zanedrys/IPAD/Polargraph/Polargraph 2017-11-01/processing-source/Processing libraries/diewald_CV_kit/examples/colorize_pattern/data/diewald_CV_kit_pattern4colorizer_v6.jpg

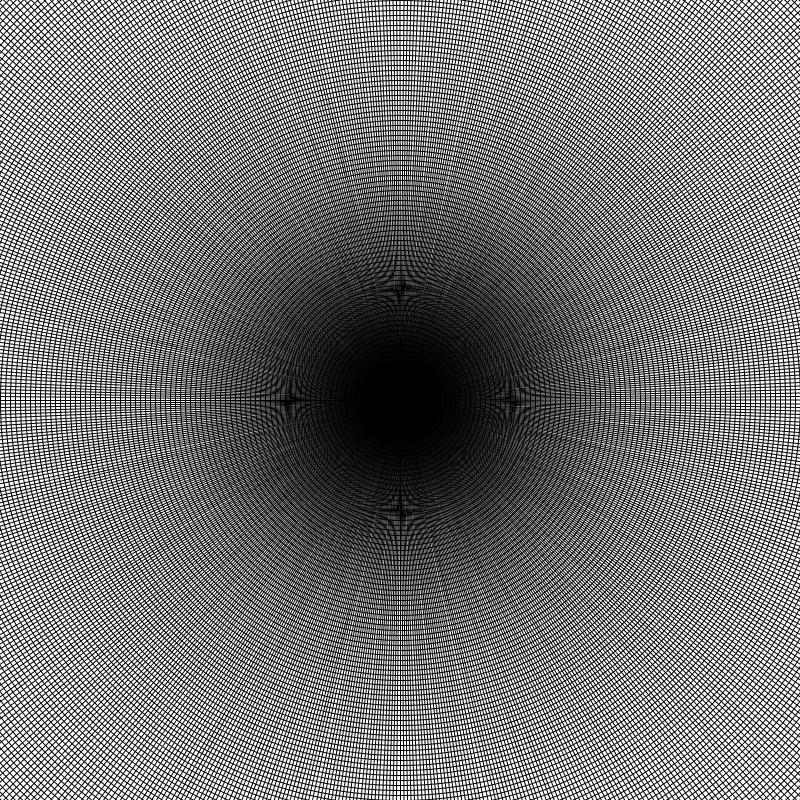
Polargraph/Polargraph 2017-11-01/processing-source/Processing libraries/diewald_CV_kit/examples/colorize_pattern/data/diewald_CV_kit_pattern4colorizer_v6.jpg
