zanedrys/IPAD/Polargraph/Polargraph 2017-11-01/processing-source/Processing libraries/diewald_CV_kit/examples/extract_hands/data/diewald_CV_kit_two_hands_640x480.jpg

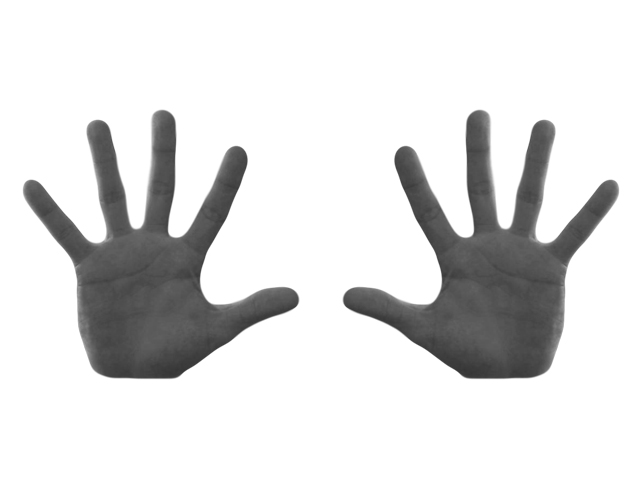
Polargraph/Polargraph 2017-11-01/processing-source/Processing libraries/diewald_CV_kit/examples/extract_hands/data/diewald_CV_kit_two_hands_640x480.jpg
