zanedrys/IPAD/Polargraph/Polargraph 2017-11-01/processing-source/Processing libraries/diewald_CV_kit/examples/kinect_3D/SCREENSHOT/diewald_CV_kit_kinect_3D_hand.jpg

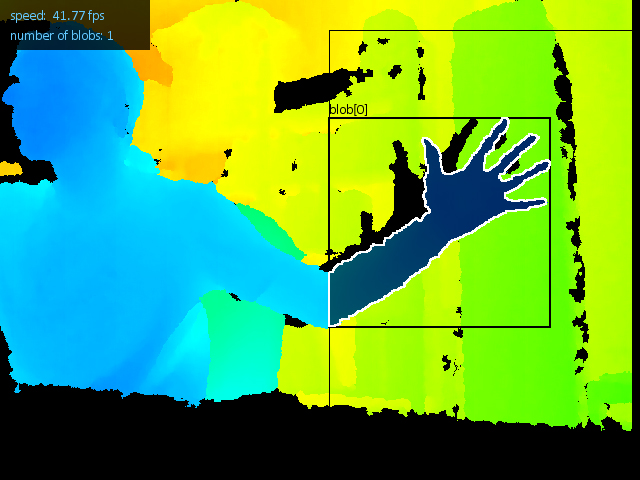
Polargraph/Polargraph 2017-11-01/processing-source/Processing libraries/diewald_CV_kit/examples/kinect_3D/SCREENSHOT/diewald_CV_kit_kinect_3D_hand.jpg
