zanedrys/IPAD/Polargraph/Polargraph 2017-11-01/processing-source/Processing libraries/diewald_CV_kit/examples/kinect_3D_pointcloud/data/diewald_CV_kit_marker_domino_4.jpg

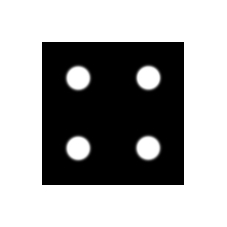
Polargraph/Polargraph 2017-11-01/processing-source/Processing libraries/diewald_CV_kit/examples/kinect_3D_pointcloud/data/diewald_CV_kit_marker_domino_4.jpg
