zanedrys/IPAD/Polargraph/Polargraph 2017-11-01/processing-source/Processing libraries/diewald_CV_kit/examples/simple_blobs/SCREENSHOT/diewald_CV_kit_simple_blobs.jpg

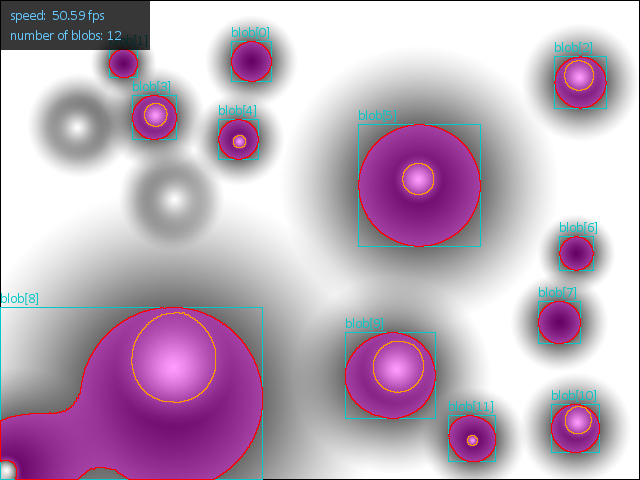
Polargraph/Polargraph 2017-11-01/processing-source/Processing libraries/diewald_CV_kit/examples/simple_blobs/SCREENSHOT/diewald_CV_kit_simple_blobs.jpg
