zanedrys/IPAD/Polargraph/Polargraph 2017-11-01/processing-source/Processing libraries/diewald_CV_kit/examples/webcam_marker_domino/data/diewald_CV_kit_marker_domino_1.jpg

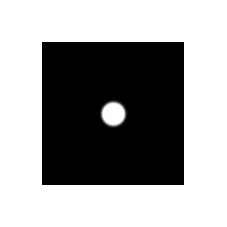
Polargraph/Polargraph 2017-11-01/processing-source/Processing libraries/diewald_CV_kit/examples/webcam_marker_domino/data/diewald_CV_kit_marker_domino_1.jpg
