zanedrys/IPAD/Processing 2.2.1/processing-2.2.1/modes/java/examples/Basics/Image/Alphamask/data/mask.jpg

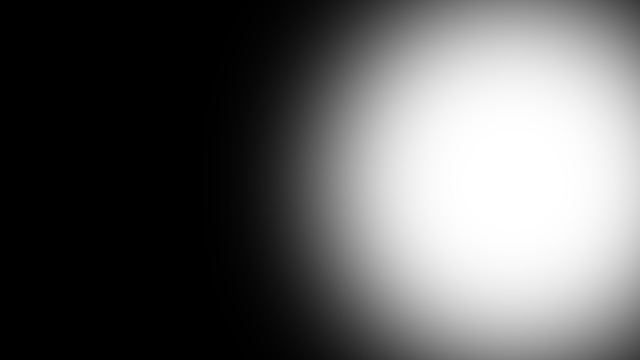
Processing 2.2.1/processing-2.2.1/modes/java/examples/Basics/Image/Alphamask/data/mask.jpg
