zanedrys/IPAD/Processing 2.2.1/processing-2.2.1/modes/java/examples/Basics/Image/Alphamask/data/moonwalk.jpg

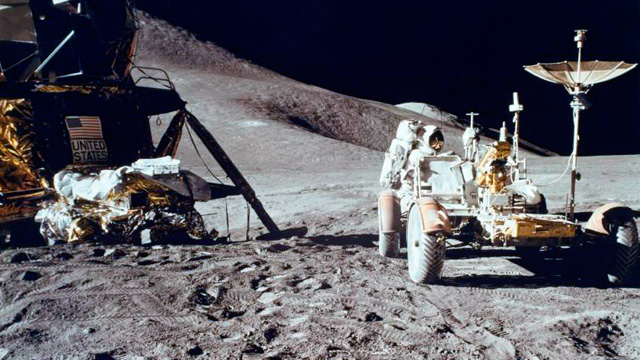
Processing 2.2.1/processing-2.2.1/modes/java/examples/Basics/Image/Alphamask/data/moonwalk.jpg
