zanedrys/IPAD/Processing 2.2.1/processing-2.2.1/modes/java/examples/Basics/Image/RequestImage/data/PT_anim0004.gif

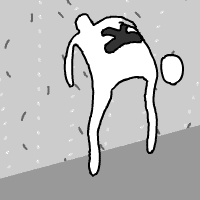
Processing 2.2.1/processing-2.2.1/modes/java/examples/Basics/Image/RequestImage/data/PT_anim0004.gif
