zanedrys/IPAD/Processing 2.2.1/processing-2.2.1/modes/java/examples/Basics/Shape/LoadDisplayOBJ/data/rocket.png

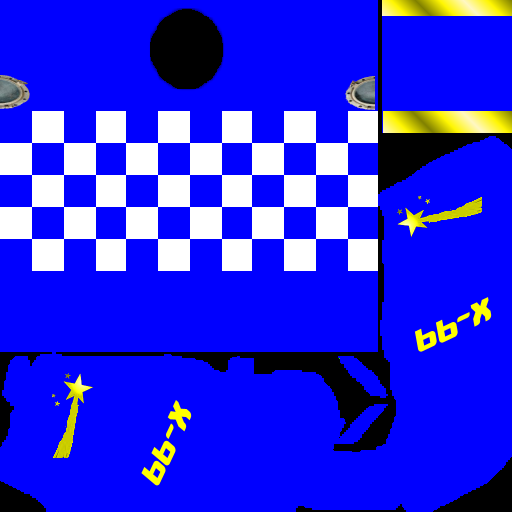
Processing 2.2.1/processing-2.2.1/modes/java/examples/Basics/Shape/LoadDisplayOBJ/data/rocket.png
