zanedrys/IPAD/Processing 2.2.1/processing-2.2.1/modes/java/examples/Books/Nature of Code/chp4_systems/Exercise_4_12_ArrayofImages/data/reflection.png

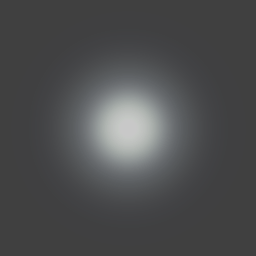
Processing 2.2.1/processing-2.2.1/modes/java/examples/Books/Nature of Code/chp4_systems/Exercise_4_12_ArrayofImages/data/reflection.png
