zanedrys/IPAD/Processing 2.2.1/processing-2.2.1/modes/java/examples/Books/Nature of Code/chp4_systems/flight404/flight404_particles_2_simple/data/emitter.png

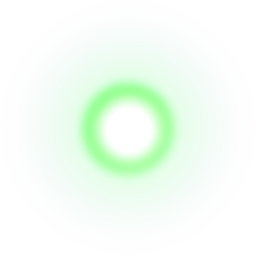
Processing 2.2.1/processing-2.2.1/modes/java/examples/Books/Nature of Code/chp4_systems/flight404/flight404_particles_2_simple/data/emitter.png
