zanedrys/IPAD/Processing 2.2.1/processing-2.2.1/modes/java/examples/Books/Nature of Code/chp6_agents/NOC_6_04_Flow_Figures/ch6_exc6.png

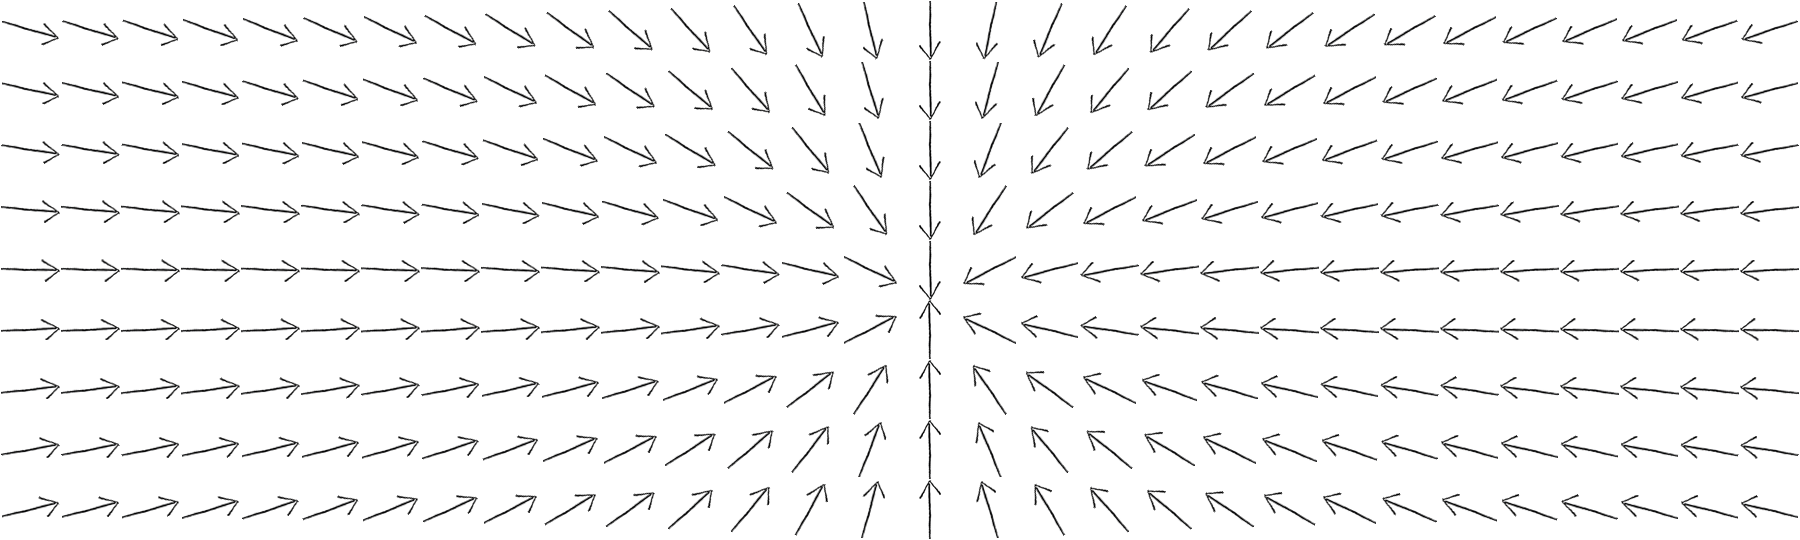
Processing 2.2.1/processing-2.2.1/modes/java/examples/Books/Nature of Code/chp6_agents/NOC_6_04_Flow_Figures/ch6_exc6.png
