zanedrys/IPAD/Processing 2.2.1/processing-2.2.1/modes/java/examples/Books/Nature of Code/chp7_CA/NOC_7_01_WolframCA_figures/rule90_low.png

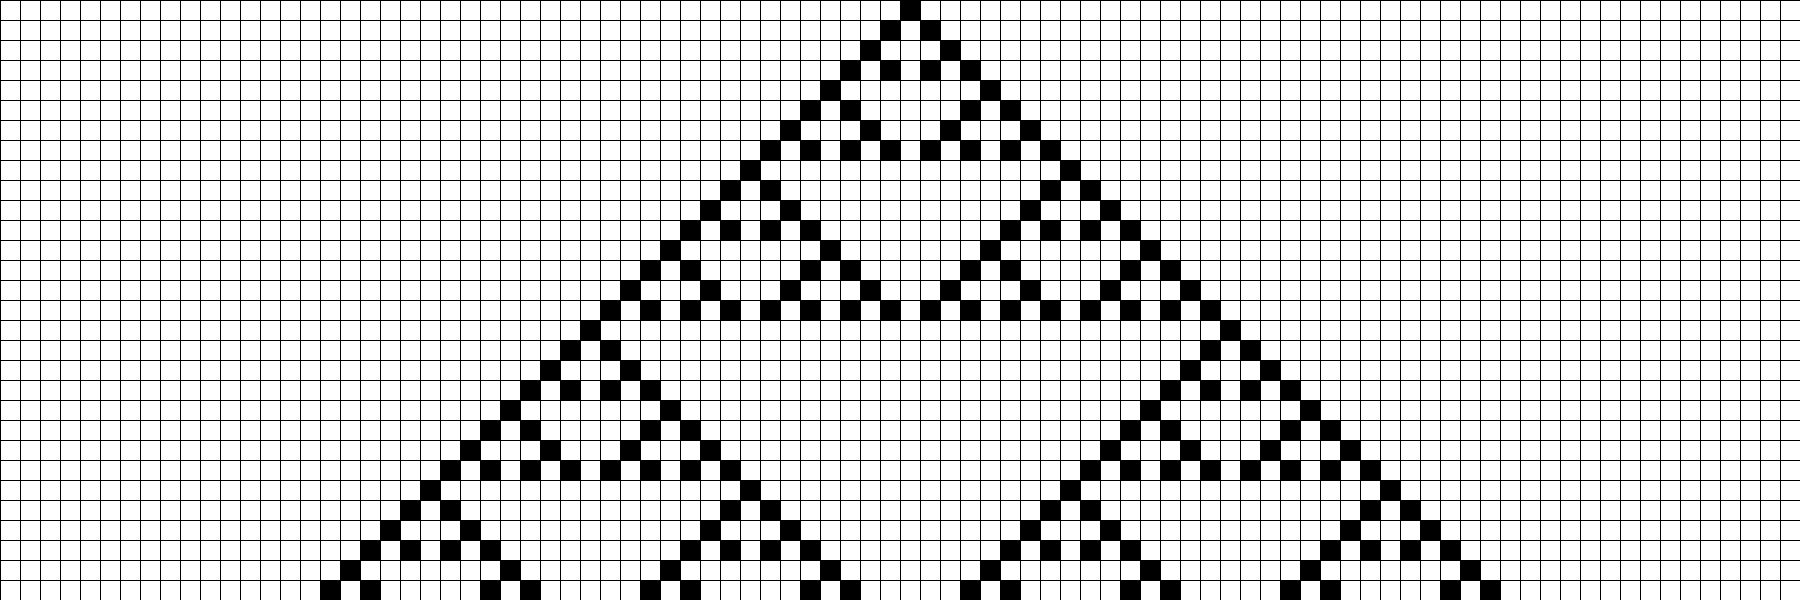
Processing 2.2.1/processing-2.2.1/modes/java/examples/Books/Nature of Code/chp7_CA/NOC_7_01_WolframCA_figures/rule90_low.png
