zanedrys/IPAD/Processing 2.2.1/processing-2.2.1/modes/java/examples/Books/Nature of Code/chp8_fractals/Figure_8_02_Mandelbrot/chapter08_02.png

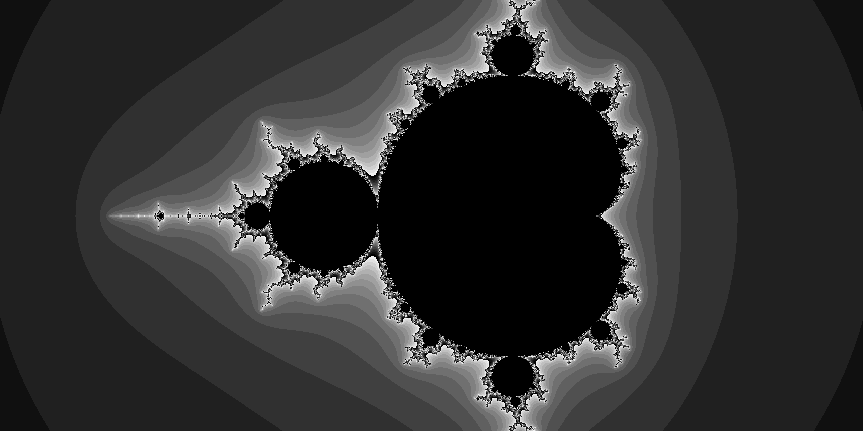
Processing 2.2.1/processing-2.2.1/modes/java/examples/Books/Nature of Code/chp8_fractals/Figure_8_02_Mandelbrot/chapter08_02.png
