zanedrys/IPAD/Processing 2.2.1/processing-2.2.1/modes/java/examples/Books/Processing Handbook/Extensions/3D/Ex_09/data/berlin-1.jpg

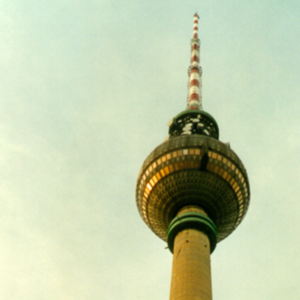
Processing 2.2.1/processing-2.2.1/modes/java/examples/Books/Processing Handbook/Extensions/3D/Ex_09/data/berlin-1.jpg
