zanedrys/IPAD/Processing 2.2.1/processing-2.2.1/modes/java/examples/Books/Processing Handbook/Illustrations/page_148/data/nyt_14.jpg

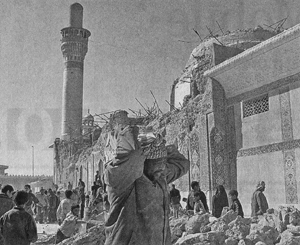
Processing 2.2.1/processing-2.2.1/modes/java/examples/Books/Processing Handbook/Illustrations/page_148/data/nyt_14.jpg
