zanedrys/IPAD/Processing 2.2.1/processing-2.2.1/modes/java/examples/Books/Processing Handbook/Illustrations/page_314/data/PT_Shifty_0005.gif

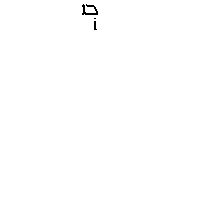
Processing 2.2.1/processing-2.2.1/modes/java/examples/Books/Processing Handbook/Illustrations/page_314/data/PT_Shifty_0005.gif
