zanedrys/IPAD/Processing 2.2.1/processing-2.2.1/modes/java/examples/Books/Processing Handbook/Synthesis/Synthesis_01_collage_01/data/nyt_06.jpg

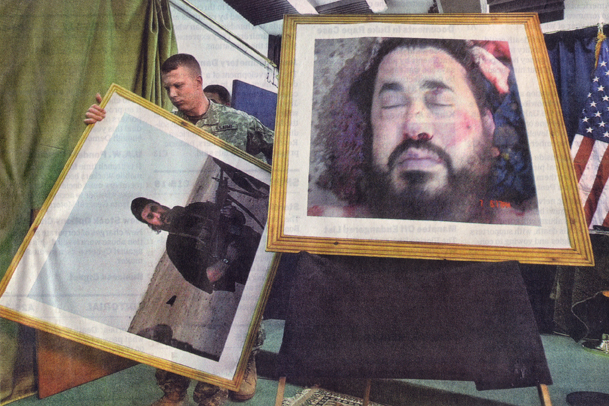
Processing 2.2.1/processing-2.2.1/modes/java/examples/Books/Processing Handbook/Synthesis/Synthesis_01_collage_01/data/nyt_06.jpg
