zanedrys/IPAD/Processing 2.2.1/processing-2.2.1/modes/java/examples/Demos/Graphics/Planets/data/planet.jpg

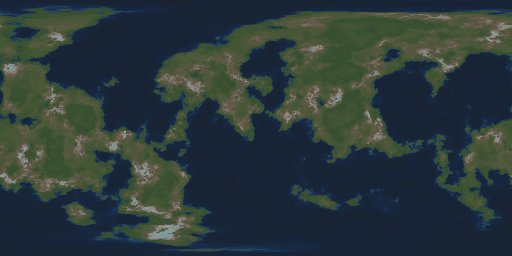
Processing 2.2.1/processing-2.2.1/modes/java/examples/Demos/Graphics/Planets/data/planet.jpg
