zanedrys/IPAD/Processing 2.2.1/processing-2.2.1/modes/java/examples/Topics/Image Processing/Blending/data/layer2.jpg

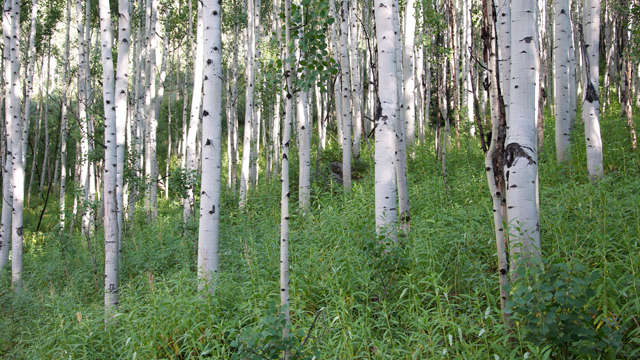
Processing 2.2.1/processing-2.2.1/modes/java/examples/Topics/Image Processing/Blending/data/layer2.jpg
