zanedrys/IPAD/Processing 2.2.1/processing-2.2.1/modes/java/examples/Topics/Image Processing/PixelArray/data/sea.jpg

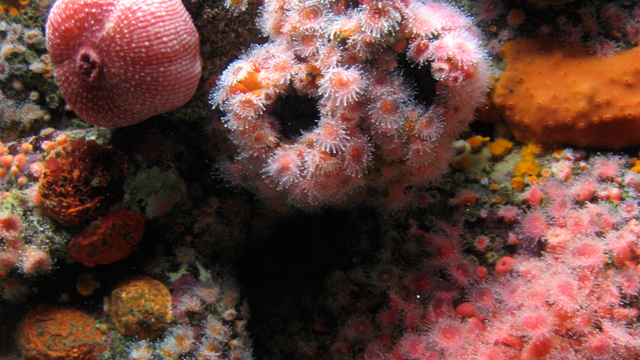
Processing 2.2.1/processing-2.2.1/modes/java/examples/Topics/Image Processing/PixelArray/data/sea.jpg
