zanedrys/IPAD/Processing 2.2.1/processing-2.2.1/modes/java/examples/Topics/Shaders/ImageMask/data/leaves.jpg

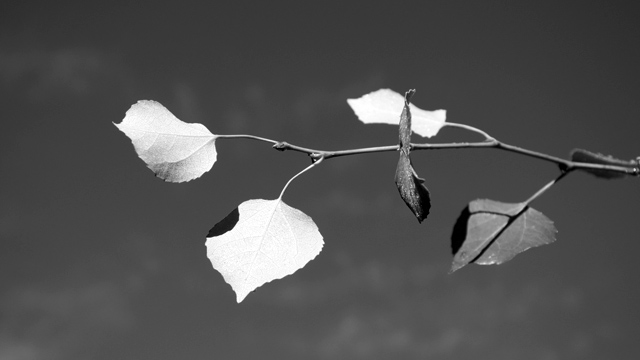
Processing 2.2.1/processing-2.2.1/modes/java/examples/Topics/Shaders/ImageMask/data/leaves.jpg
