zanedrys/IPAD/Processing 2.2.1/processing-2.2.1/modes/java/reference/environment/images/coordinates2D3D.png

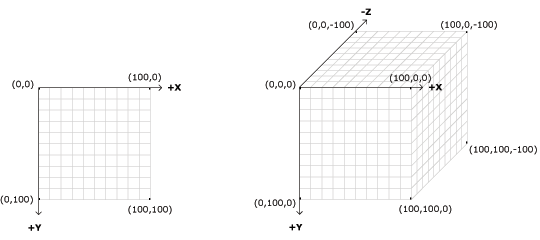
Processing 2.2.1/processing-2.2.1/modes/java/reference/environment/images/coordinates2D3D.png
