zanedrys/IPAD/Processing 2.2.1/processing-2.2.1/modes/java/reference/environment/images/coordinates.gif

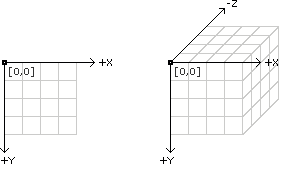
Processing 2.2.1/processing-2.2.1/modes/java/reference/environment/images/coordinates.gif
