zanedrys/IPAD/Processing 2.2.1/processing-2.2.1/modes/java/reference/img/processing-web.png

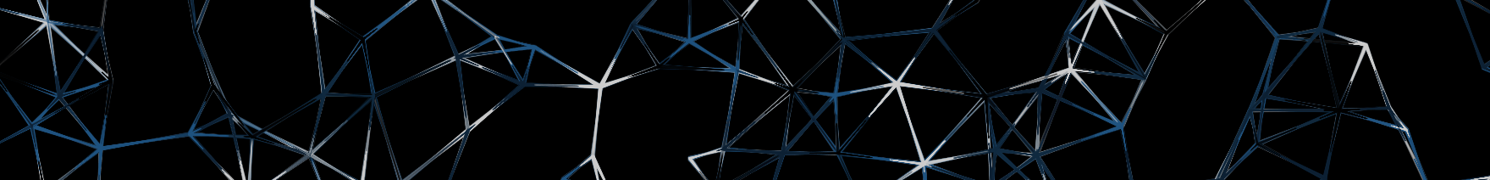
Processing 2.2.1/processing-2.2.1/modes/java/reference/img/processing-web.png
