zanedrys/IPAD/Processing 2.2.1/processing-2.2.1/modes/java/examples/Books/Getting Started/Chapter06/Ex_06_02/data/capsule.jpg

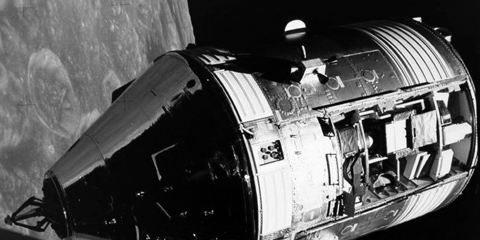
Processing 2.2.1/processing-2.2.1/modes/java/examples/Books/Getting Started/Chapter06/Ex_06_02/data/capsule.jpg
