zanedrys/IPAD/Processing 2.2.1/processing-2.2.1/modes/java/examples/Books/Getting Started/Chapter10/Ex_10_11/data/frame-0010.png

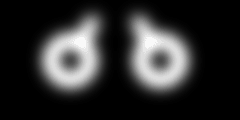
Processing 2.2.1/processing-2.2.1/modes/java/examples/Books/Getting Started/Chapter10/Ex_10_11/data/frame-0010.png
