zanedrys/IPAD/Processing 2.2.1/processing-2.2.1/modes/java/examples/Books/Getting Started/Robots/Robot4_Media/data/alpine.png

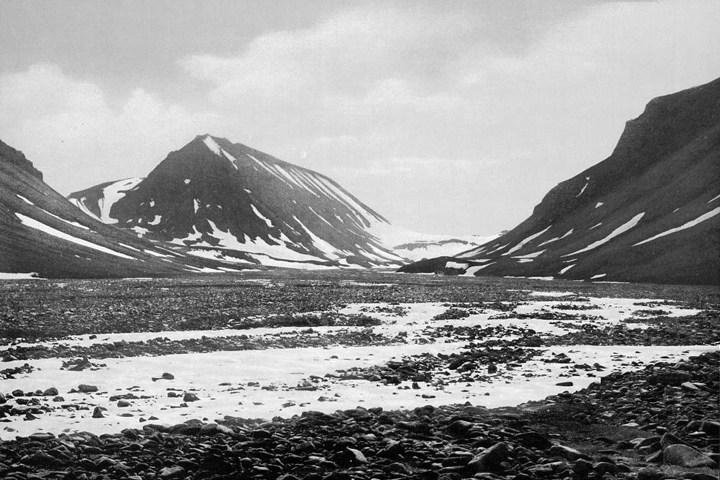
Processing 2.2.1/processing-2.2.1/modes/java/examples/Books/Getting Started/Robots/Robot4_Media/data/alpine.png
