zanedrys/IPAD/Processing 2.2.1/processing-2.2.1/modes/java/examples/Books/Visualizing Data/ch03-usmap/step00_show_map/data/map.png

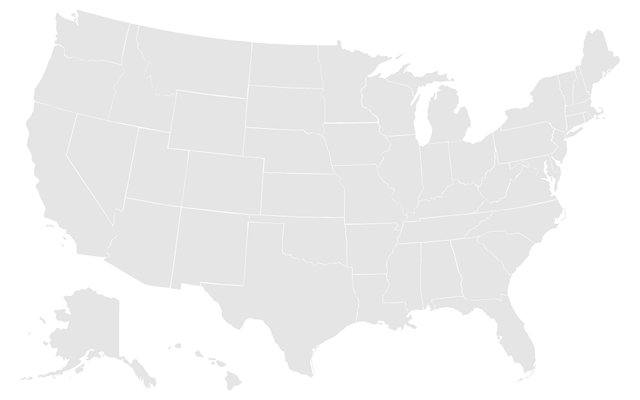
Processing 2.2.1/processing-2.2.1/modes/java/examples/Books/Visualizing Data/ch03-usmap/step00_show_map/data/map.png
