zanedrys/IPAD/Processing 2.2.1/processing-2.2.1/modes/java/examples/Books/Visualizing Data/ch03-usmap/step04_fig4_blue_green/data/map.png

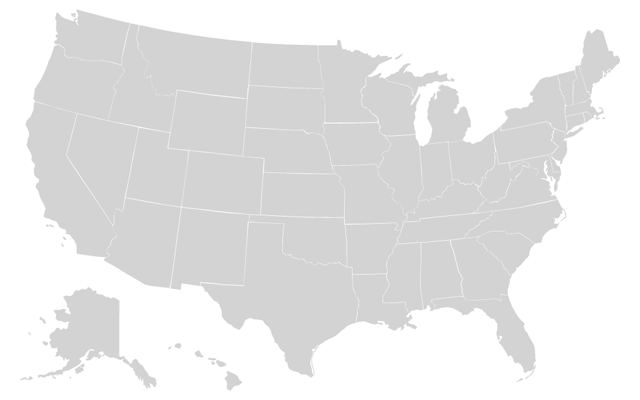
Processing 2.2.1/processing-2.2.1/modes/java/examples/Books/Visualizing Data/ch03-usmap/step04_fig4_blue_green/data/map.png
