zanedrys/IPAD/Wiring Diagram.jpg

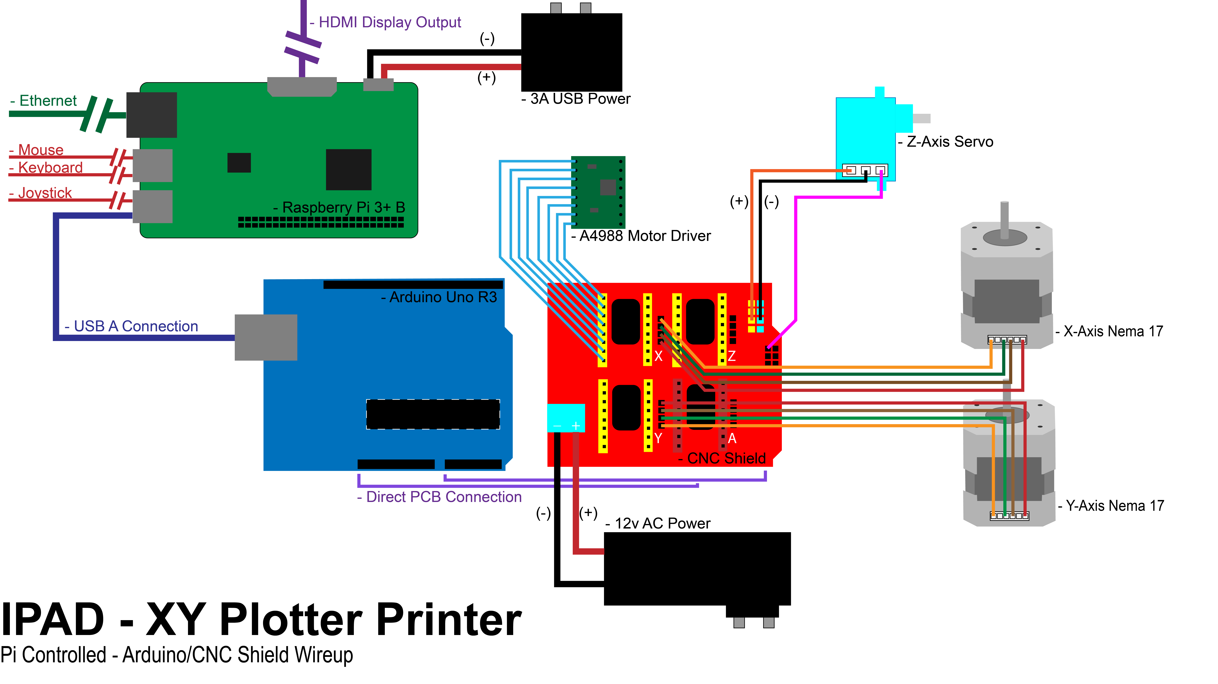
Wiring Diagram.jpg
