zanedrys/IPAD/Processing 2.2.1/processing-2.2.1/modes/java/examples/Basics/Structure/CreateGraphics/data/test.jpg

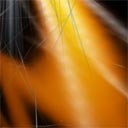
Processing 2.2.1/processing-2.2.1/modes/java/examples/Basics/Structure/CreateGraphics/data/test.jpg
