zanedrys/IPAD/Polargraph/Polargraph 2017-11-01/processing-source/Processing libraries/diewald_CV_kit/examples/polylinesimplifier/polylinesimplifier.pde

//---------------------------------------------------------
//
// author: thomas diewald
// date: 06.09.2011
//
// example how to use diewald_CV_kit.blobdetection.
//
// -------------------------------------------------------
// interaction:
//
// mouseX - defines the number of polyline-simplification steps
//---------------------------------------------------------

import java.util.Locale;
import diewald_CV_kit.libraryinfo.*;
import diewald_CV_kit.utility.*;
import diewald_CV_kit.blobdetection.*;




PFont font;
PImage sample_img;
int size_x, size_y;

BlobDetector blob_detector;

public void setup() {

  String image_path = sketchPath+"/data/";

  sample_img = loadImage(image_path + "diewald_CV_kit_hand_640x480.jpg");

  size_x = sample_img.width;
  size_y = sample_img.height;
  size(size_x, size_y);

  sample_img.loadPixels();

  blob_detector = new BlobDetector( size_x, size_y);
  blob_detector.setResolution(1);
  blob_detector.computeContours(true);
  blob_detector.computeBlobPixels(true);
  blob_detector.setMinMaxPixels(10*10, size_x*size_y);
  blob_detector.setBLOBable(new BLOBable_Hands(this, sample_img));

  font = createFont("Calibri", 14);
  textFont(font);
  frameRate(200);
}




public void draw() {
  background(255);
  //    blob_detector.takeEveryNthPixel((int) map(mouseX, 0, width, 0, 20));
  image(sample_img, 0, 0);

  blob_detector.setResolution(1);

  //update the blob_detector with the new pixelvalues
  blob_detector.update();

  // get a list of all the blobs
  ArrayList<Blob> blob_list = blob_detector.getBlobs();


  // iterate through the blob_list
  for (int blob_idx = 0; blob_idx < blob_list.size(); blob_idx++ ) {

    // get the current blob from the blob-list
    Blob blob = blob_list.get(blob_idx);
    //      System.out.println("number of pixels = " +blob.getNumberOfPixels() );
    // get the list of all the contours from the current blob
    ArrayList<Contour> contour_list = blob.getContours();

    // iterate through the contour_list
    for (int contour_idx = 0; contour_idx < contour_list.size(); contour_idx++ ) {

      // get the current contour from the contour-list
      Contour contour = contour_list.get(contour_idx);

      // get the current boundingbox from the current contour
      BoundingBox bb = contour.getBoundingBox();


      // handle the first contour (outer contour = contour_idx == 0) different to the inner contours
      if ( contour_idx == 0) {

        // draw the boundingbox
        drawBoundingBox(bb, color(0), 1);
        // draw the blob-id
        fill(0);
        text("blob["+blob_idx+"]", bb.xMin(), bb.yMin()- textDescent()*2);


        // draw the contour
        drawContour(contour.getPixels(), color(255, 0, 0), color(0, 255, 0, 50), !true, 1); 




        // example how to simplify a contour
        int repeat_simplifying = (int) map(mouseX, 0, width, 0, 50);
        // can improve speed, if the contour is needed for further work
        ArrayList<Pixel> contour_simple = Polyline.SIMPLIFY(contour, 2, 1);
        // repeat the simplifying process a view more times
        for (int simple_cnt = 0; simple_cnt < repeat_simplifying; simple_cnt++) {
          contour_simple= Polyline.SIMPLIFY(contour_simple, 2, simple_cnt);
        }
        // draw the simplified contour
        drawContour(contour_simple, color(0, 200, 200), color(0, 0, 200, 50), false, 2);
        drawPoints(contour_simple, color(0, 200, 200), 11);




        // generate a convex hull object
        ConvexHullDiwi convex_hull = new ConvexHullDiwi();
        // calculate the convex hull, based on the contour-list
        convex_hull.update(contour_simple);
        //draw the convex hull
        drawConvexHull(convex_hull, color(0, 255, 0), 2);
        drawConvexHullPoints(convex_hull, color(0, 255, 0), 25);
      } 
      else {
        // we don't handle inner contours here
      }
    }
  }


  fill(255, 200); 
  noStroke();
  rect(0, 0, 120, 50);
  printlnNumberOfBlobs(blob_detector);
  printlnFPS();
}
